rorkela/macropad/firmware/macropad/src/figures.h

#pragma once

#define IITH_WIDTH 20
#define IITH_HEIGHT_8 3

static const uint8_t iith[IITH_HEIGHT_8][IITH_WIDTH] = {
    {
        0b11000000, 0b00000000, 0b10000000, 0b00000000,
        0b10000000, 0b00000000, 0b10011100, 0b00111110,
        0b01111111, 0b01111111, 0b01111111, 0b00111110,
        0b10011100, 0b00000000, 0b10000000, 0b00000000,
        0b10000000, 0b00000000, 0b11000000, 0b00000000
    },
    {
        0b11111111, 0b00000000, 0b11111111, 0b00000000,
        0b11111111, 0b00000000, 0b11111111, 0b11111111,
        0b11111110, 0b00000000, 0b11111110, 0b11111111,
        0b11111111, 0b00000000, 0b11111111, 0b00000000,
        0b11111111, 0b00000000, 0b11111111, 0b00000000
    },
    {
        0b00001111, 0b00000000, 0b00000111, 0b00000000,
        0b00000111, 0b00000000, 0b00000111, 0b00000011,
        0b00000001, 0b00000000, 0b00000001, 0b00000011,
        0b00000111, 0b00000000, 0b00000111, 0b00000000,
        0b00000111, 0b00000000, 0b00001111, 0b00000000
    }
};
