rorkela/macropad/firmware/tests/keytest/keytest.c

#include <libopencm3/stm32/rcc.h>
#include <libopencm3/stm32/gpio.h>

int main(void)
{
	rcc_clock_setup_pll(&rcc_hsi_configs[RCC_CLOCK_HSI_24MHZ]);

	rcc_periph_clock_enable(RCC_GPIOC);
	rcc_periph_clock_enable(RCC_GPIOA);

	gpio_set_mode(GPIOA, GPIO_MODE_INPUT,
		GPIO_CNF_INPUT_PULL_UPDOWN, GPIO12);
	gpio_set(GPIOA, GPIO12);

	gpio_set_mode(GPIOC, GPIO_MODE_OUTPUT_2_MHZ,
		GPIO_CNF_OUTPUT_PUSHPULL, GPIO13);

	while (1) {
		if(!gpio_get(GPIOA, GPIO12)) {
			gpio_set(GPIOC, GPIO13);
		}
		else {
			gpio_clear(GPIOC, GPIO13);
		}
	}
}
